gorkemguven/ESP32-S3-4Layer-CoreBoard/Git_Hub_ESP32/ESP-32_Design_Görkem_Güven.kicad_sch

## KiCad design Git_Hub_ESP32/ESP-32_Design_Görkem_Güven.kicad_sch (2026-03-22)

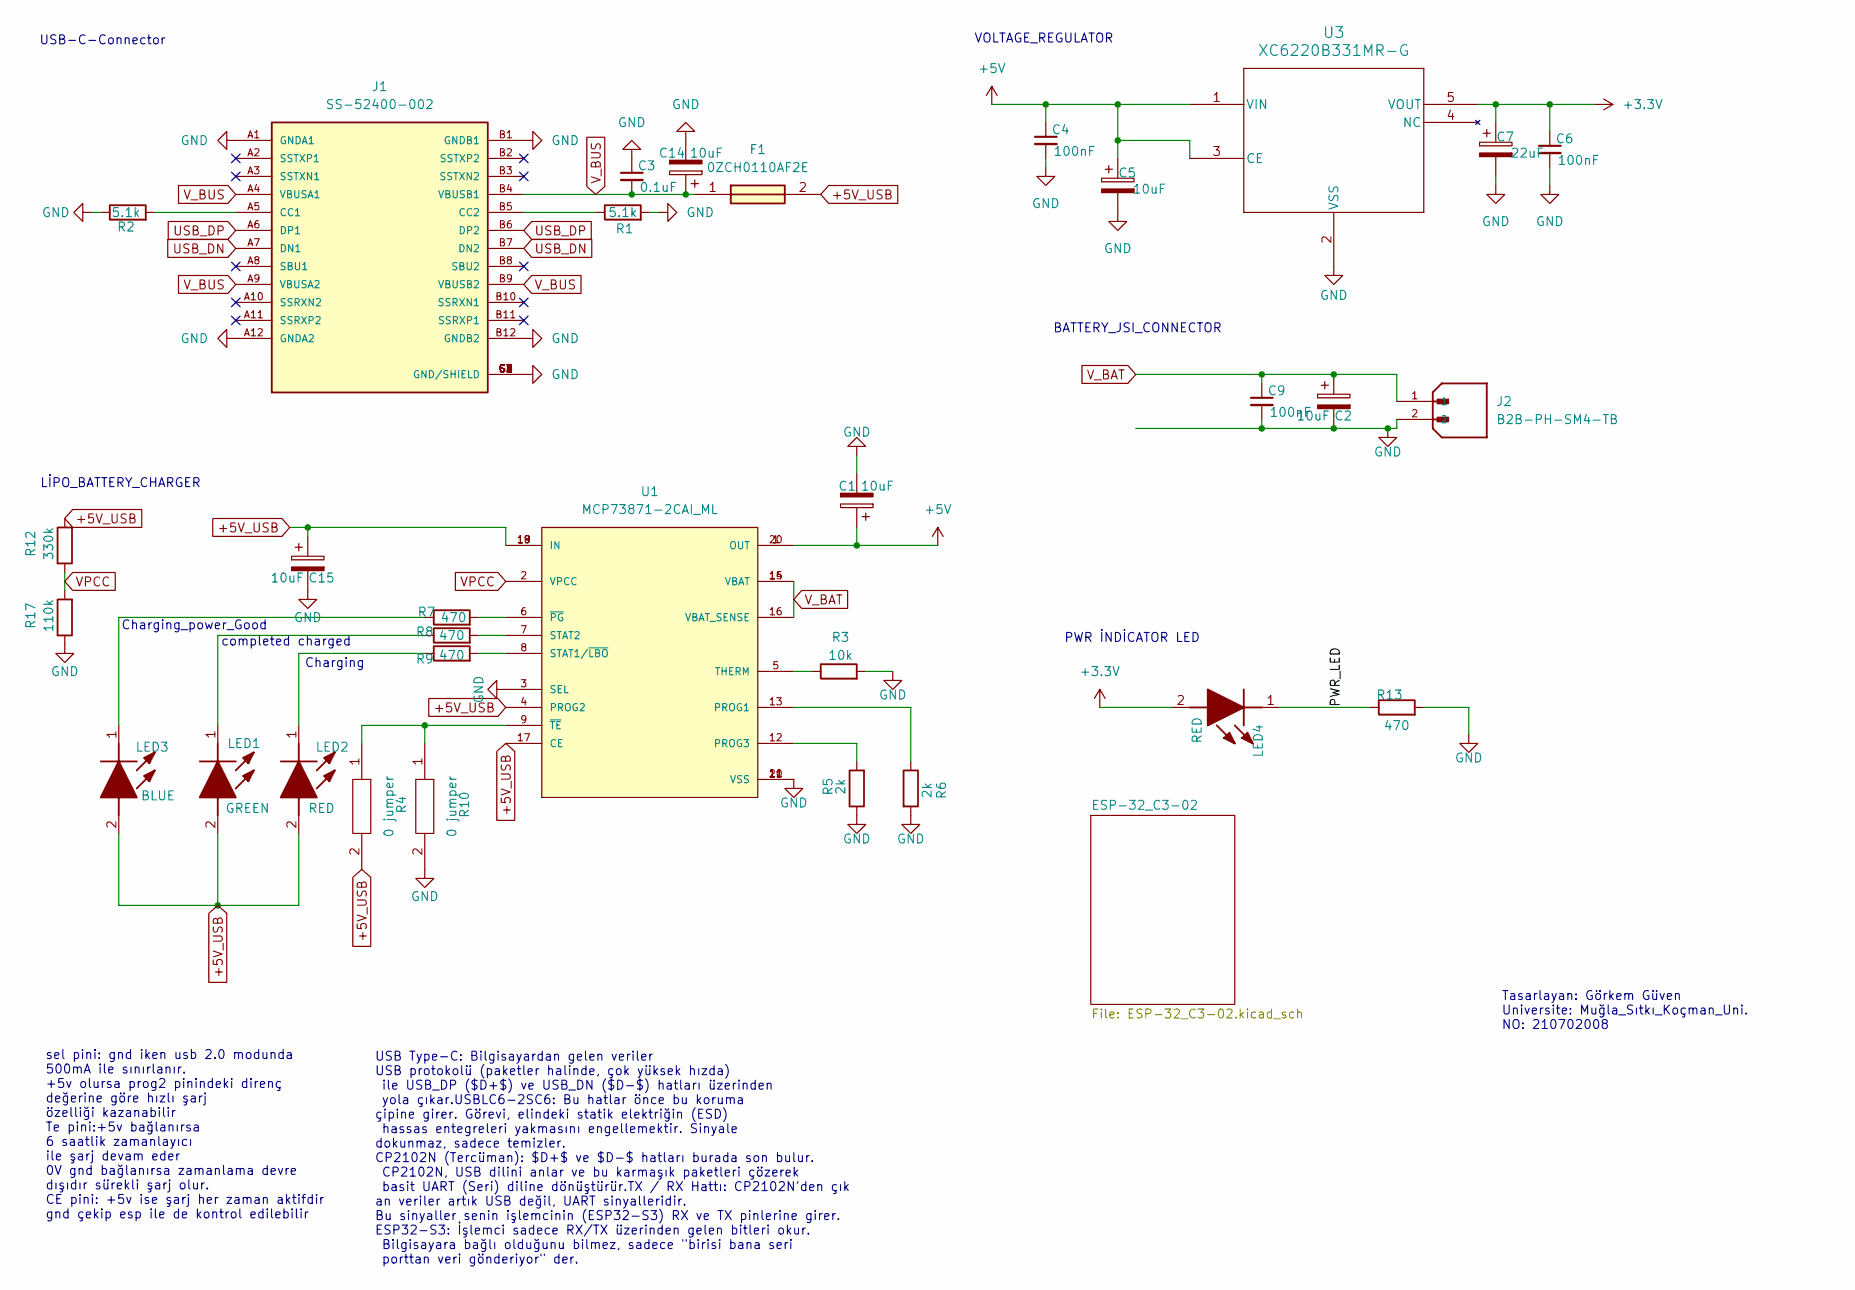
[picture p6: schematic ESP-32_Design_Görkem_Güven.kicad_sch]

Parts:
C1, C2, C5, C14, C15: 10uF; T491A
C3: 0.1uF; C_0805_2012Metric
C4, C6, C9: 100nF; C_0805_2012Metric
C7: 22uF; T491A
F1: 0ZCH0110AF2E; FUSC3226X100N; Manufacturer_Part_Number 0ZCH0110AF2E
J1: SS-52400-002; BELFUSE_SS-52400-002; PARTREV A0
J2: B2B-PH-SM4-TB; JST_B2B-PH-SM4-TB; PARTREV N/A
LED1: GREEN; LEDC2012X120N; Manufacturer_Part_Number LTST-C170GKT; Mouser Part Number 859-LTST-C170GKT
LED2, LED4: RED; LEDC2012X120N; Manufacturer_Part_Number LTST-C170KRKT; Mouser Part Number 859-LTST-C170KRKT
LED3: BLUE; LEDC2012X120N; Manufacturer_Part_Number LTST-C170TBKT; Mouser Part Number 859-LTST-C170TBKT
R1, R2: 5.1k; R_0805_2012Metric
R3: 10k; R_0805_2012Metric
R4, R10: 0 jumper; R_0805_2012Metric; Manufacturer_Part_Number ERJ12ZY0R00U
R5, R6: 2k; R_0805_2012Metric
R7, R8, R9, R13: 470; R_0805_2012Metric
R12: 330k; R_0805_2012Metric
R17: 110k; R_0805_2012Metric
U1: MCP73871-2CAI_ML; QFN50P400X400X100-21N; PARTREV D
U3: XC6220B331MR-G; IC_XC8107AC20MR-G

Connections:
+3.3V: C6.1, C7.1, LED4.2 (A), U3.5 (VOUT)
+5V: C1.1, C4.1, C5.1, U1.1 (OUT), U1.20 (OUT), U3.1 (VIN), U3.3 (CE)
+5V_USB: C15.1, F1.2, LED1.2 (A), LED2.2 (A), LED3.2 (A), R4.2, R12.2, U1.4 (PROG2), U1.17 (CE), U1.18 (IN), U1.19 (IN)
GND: C1.2, C2.2, C3.1, C4.2, C5.2, C6.2, C7.2, C9.2, C14.2, C15.2, J1.A1 (GNDA1), J1.A12 (GNDA2), J1.B1 (GNDB1), J1.B12 (GNDB2), J1.G1 (GND/SHIELD), J1.G2 (GND/SHIELD), J1.G3 (GND/SHIELD), J1.G4 (GND/SHIELD), J1.S1 (GND/SHIELD), J1.S2 (GND/SHIELD), J1.S3 (GND/SHIELD), J1.S4 (GND/SHIELD), J2.2, R1.2, R2.1, R3.2, R5.1, R6.2, R10.2, R13.2, R17.1, U1.3 (SEL), U1.10 (VSS), U1.11 (VSS), U1.21 (VSS), U3.2 (VSS)
unnamed: J1.A5 (CC1), R2.2
unnamed: J1.B5 (CC2), R1.1
unnamed: LED1.1 (K), R8.1
unnamed: LED2.1 (K), R9.1
unnamed: LED3.1 (K), R7.1
unnamed: R3.1, U1.5 (THERM)
unnamed: R5.2, U1.12 (PROG3)
unnamed: R6.1, U1.13 (PROG1)
unnamed: R7.2, U1.6 (~PG)
unnamed: R8.2, U1.7 (STAT2)
unnamed: R9.2, U1.8 (STAT1/~LBO)
unnamed: R4.1, R10.1, U1.9 (~TE)
PWR_LED: LED4.1 (K), R13.1
USB_DN: J1.A7 (DN1), J1.B7 (DN2)
USB_DP: J1.A6 (DP1), J1.B6 (DP2)
VPCC: R12.1, R17.2, U1.2 (VPCC)
V_BAT: C2.1, C9.1, J2.1, U1.14 (VBAT), U1.15 (VBAT), U1.16 (VBAT_SENSE)
V_BUS: C3.2, C14.1, F1.1, J1.A4 (VBUSA1), J1.A9 (VBUSA2), J1.B4 (VBUSB1), J1.B9 (VBUSB2)

Notes on the sheet:
Charging
Tasarlayan: Görkem Güven Universite: Muğla_Sıtkı_Koçman_Uni. NO: 210702008
completed charged
Charging_power_Good
USB Type-C: Bilgisayardan gelen veriler USB protokolü (paketler halinde, çok yüksek hızda) ile USB_DP ($D+$) ve USB_DN ($D-$) hatları üzerinden yola çıkar.USBLC6-2SC6: Bu hatlar önce bu koruma çipine girer. Görevi, elindeki statik elektriğin (ESD) hassas entegreleri yakmasını engellemektir. Sinyale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
sel pini: gnd iken usb 2.0 modunda 500mA ile sınırlanır. +5v olursa prog2 pinindeki direnç değerine göre hızlı şarj özelliği kazanabilir Te pini:+5v bağlanırsa 6 saatlik zamanlayıcı ile şarj devam eder 0V gnd bağlanırsa zamanlama devre dışıdır sürekli şarj olur. CE pini: +5v ise şarj her zaman akti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
BATTERY_JSI_CONNECTOR
PWR İNDİCATOR LED
LİPO_BATTERY_CHARGER
USB-C-Connector
VOLTAGE_REGULATOR
