gorkemguven/ESP32-S3-4Layer-CoreBoard/Git_Hub_ESP32/Sensors.kicad_sch

## KiCad design Git_Hub_ESP32/Sensors.kicad_sch (2026-03-22)

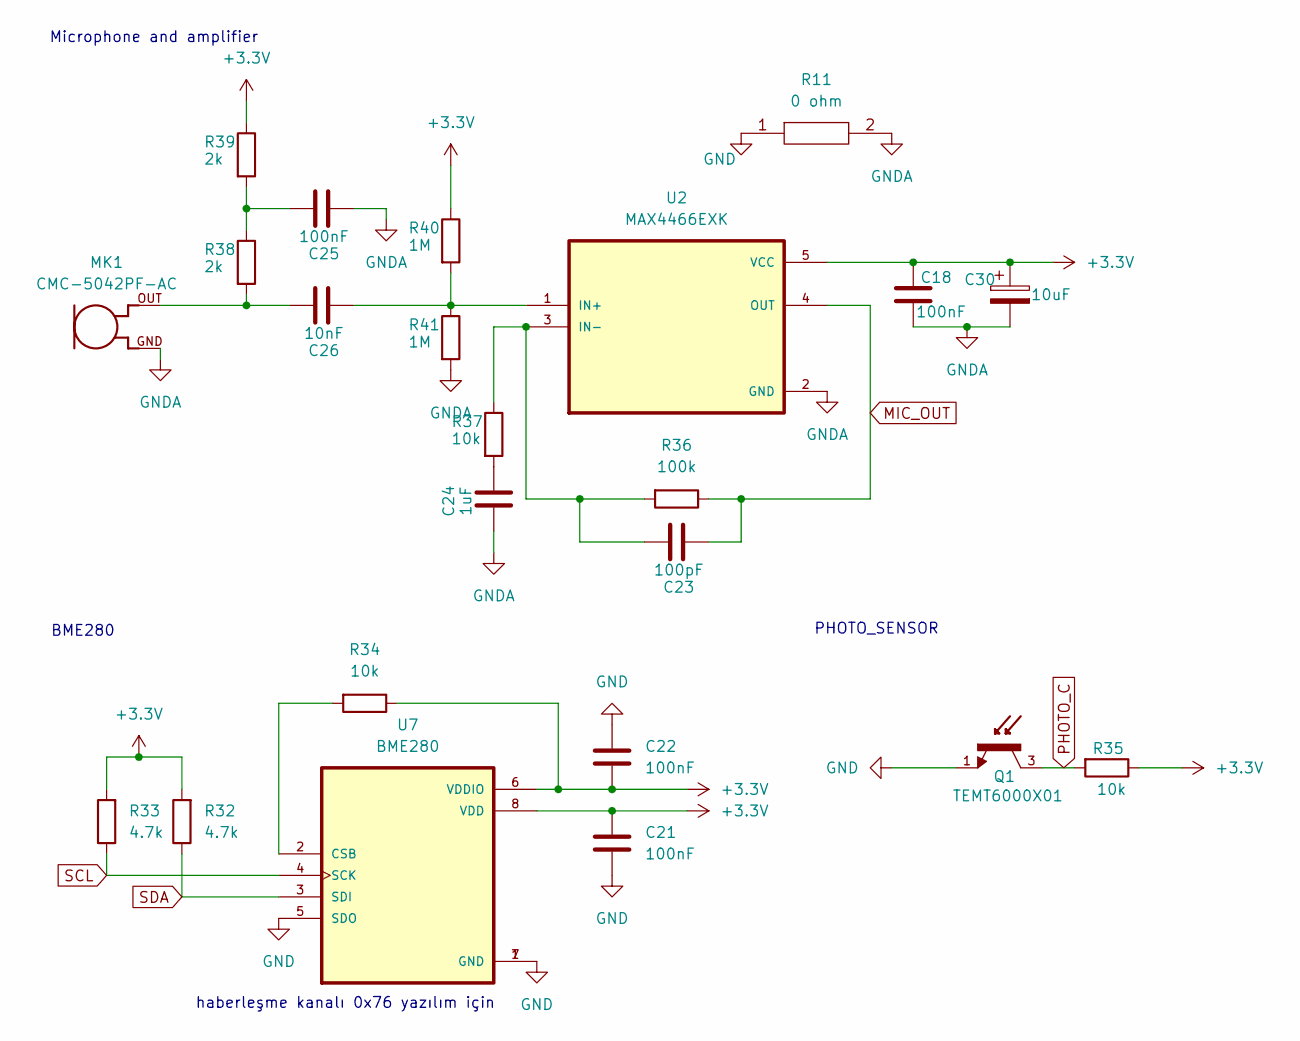
[picture p7: schematic Sensors.kicad_sch]

Parts:
C18, C21, C22, C25: 100nF; C_0805_2012Metric
C23: 100pF; C_0805_2012Metric
C24: 1uF; C_0805_2012Metric
C26: 10nF; C_0805_2012Metric
C30: 10uF; T491A
MK1: CMC-5042PF-AC; CUI_CMC-5042PF-AC
Q1: TEMT6000X01; TRANS_TEMT6000X01; PARTREV 1.9
R11: 0 ohm; R_0805_2012Metric; Manufacturer_Part_Number ERJ12ZY0R00U
R32, R33: 4.7k; R_0805_2012Metric
R34, R35, R37: 10k; R_0805_2012Metric
R36: 100k; R_0805_2012Metric
R38, R39: 2k; R_0805_2012Metric
R40, R41: 1M; R_0805_2012Metric
U2: MAX4466EXK; SOT65P210X110-5N
U7: BME280; PSON65P250X250X100-8N

Connections:
+3.3V: C18.1, C21.1, C22.2, C30.1, R32.2, R33.2, R34.1, R35.1, R39.1, R40.1, U2.5 (VCC), U7.6 (VDDIO), U7.8 (VDD)
GND: C21.2, C22.1, Q1.1, R11.1, U7.1 (GND), U7.5 (SDO), U7.7 (GND)
GNDA: C18.2, C24.2, C25.2, C30.2, MK1.GND, R11.2, R41.2, U2.2 (GND)
MIC_OUT: C23.2, R36.1, U2.4 (OUT)
unnamed: C23.1, R36.2, R37.1, U2.3 (IN-)
unnamed: C24.1, R37.2
unnamed: C25.1, R38.1, R39.2
unnamed: C26.1, MK1.OUT, R38.2
unnamed: C26.2, R40.2, R41.1, U2.1 (IN+)
unnamed: R34.2, U7.2 (CSB)
PHOTO_C: Q1.3, R35.2
SCL: R33.1, U7.4 (SCK)
SDA: R32.1, U7.3 (SDI)

Notes on the sheet:
BME280
Microphone and amplifier
haberleşme kanalı 0x76 yazılım için
PHOTO_SENSOR
