gorkemguven/ESP32-S3-4Layer-CoreBoard/Git_Hub_ESP32/user_interference.kicad_sch

## KiCad design Git_Hub_ESP32/user_interference.kicad_sch (2026-03-22)

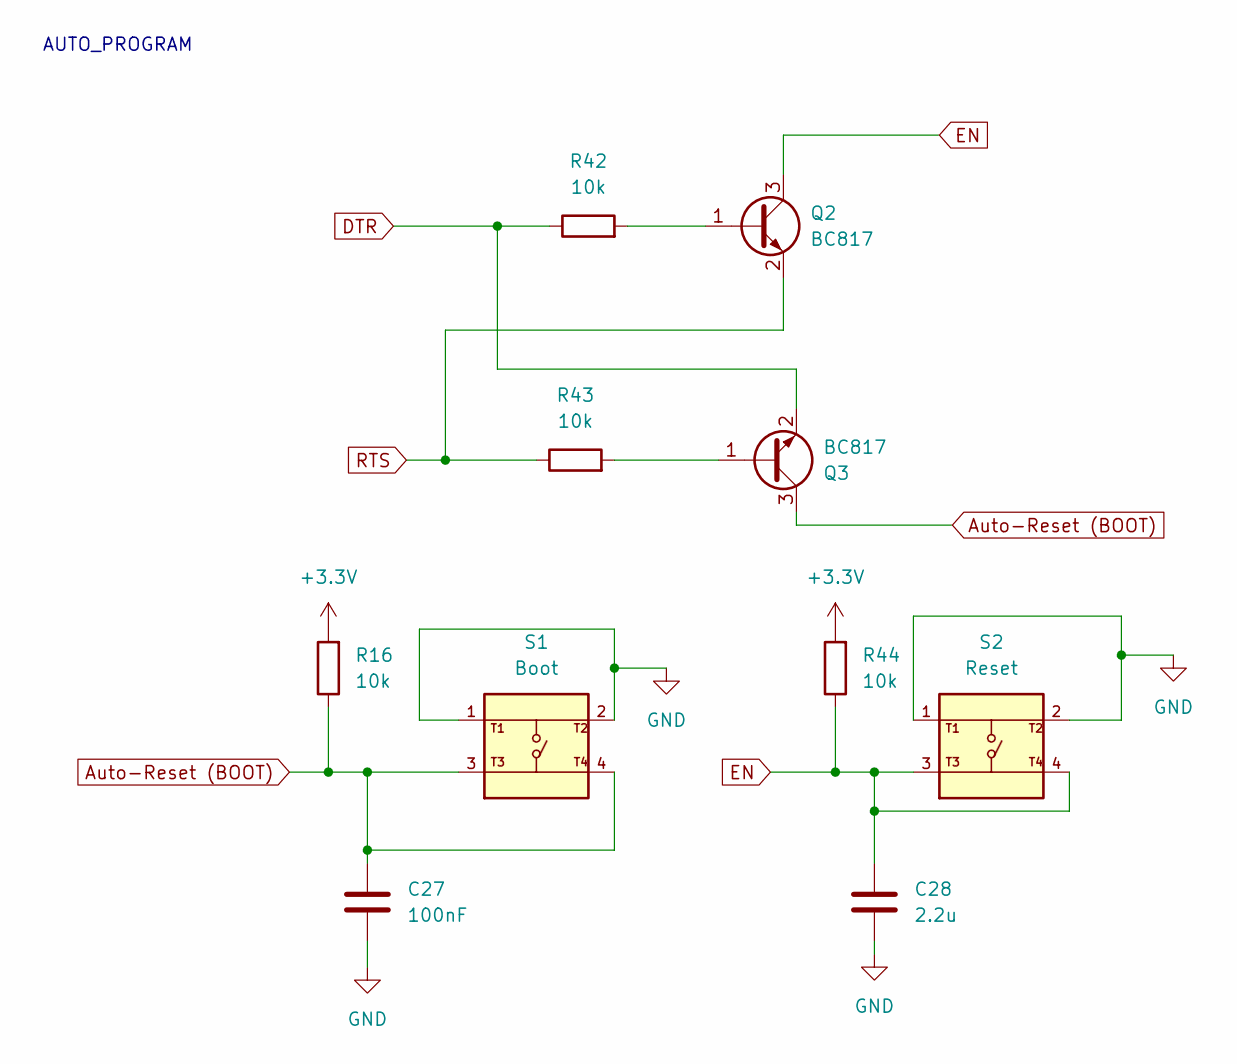
[picture p8: schematic user_interference.kicad_sch]

Parts:
C27: 100nF; C_0805_2012Metric
C28: 2.2u; T491A
Q2, Q3: BC817; SOT-23
R16, R42, R43, R44: 10k; R_0805_2012Metric
S1: Boot; SW_USLPT2819DT2TR; PARTREV P
S2: Reset; SW_USLPT2819DT2TR; PARTREV P

Connections:
+3.3V: R16.2, R44.2
Auto-Reset (BOOT): C27.1, Q3.3 (C), R16.1, S1.3, S1.4
DTR: Q3.2 (E), R42.1
EN: C28.1, Q2.3 (C), R44.1, S2.3, S2.4
GND: C27.2, C28.2, S1.1, S1.2, S2.1, S2.2
unnamed: Q2.1 (B), R42.2
unnamed: Q3.1 (B), R43.2
RTS: Q2.2 (E), R43.1

Notes on the sheet:
AUTO_PROGRAM
